jeremymlong/quantizer/firmware/quantizer/dac_output_notes.h

#pragma once
#include <Arduino.h>

const static uint16_t dac_output_notes[] = {
    0,
    68,
    137,
    205,
    273,
    341,
    410,
    478,
    546,
    614,
    683,
    751,
    819,
    887,
    956,
    1024,
    1092,
    1160,
    1229,
    1297,
    1365,
    1433,
    1502,
    1570,
    1638,
    1706,
    1775,
    1843,
    1911,
    1979,
    2048,
    2116,
    2184,
    2252,
    2321,
    2389,
    2457,
    2525,
    2594,
    2662,
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
};
